tobychui/DezKVM-Go/img/2.jpg

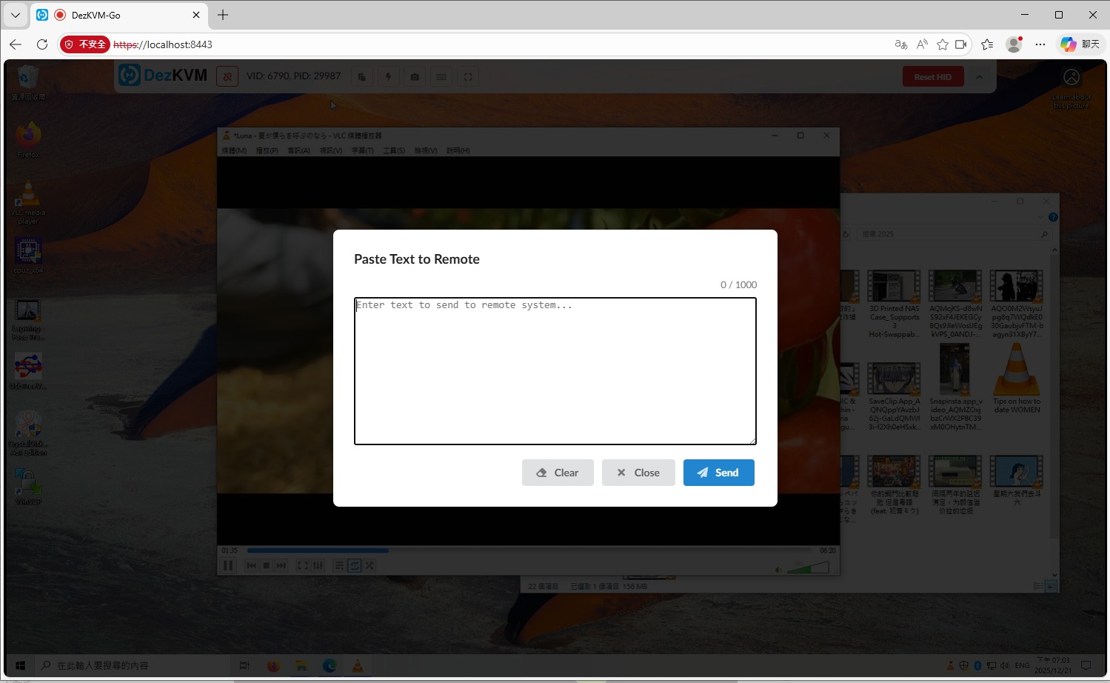
img/2.jpg
